knielsen/pcb_stm32f4_sram/pcb_sram.sch

## KiCad design pcb_sram.sch (2013-07-26)

Schematic: pcb_sram.sch

Parts:
B1: SWITCH_4PIN
C1, C2, C23, C24: 2.2u
C3, C20: 22p
C4, C8, C9, C10, C11, C12, C13, C14, C15, C16, C17, C18, C19, C22, C25, C27, C29, C30: 100n
C21: 4.7u
C26, C28: 1u
D1: SML-211UTT86
D2: SML-211YTT86
JP1: JUMPER3
L1: 30@100MHz
L2: 22@100MHz
P1, P2, P3, P4: DIL32
P6: CONN_3
P7: KNUSB
P8: SD_CARD
R1, R2: 1k
U1: STM32F40X_LQFP144
U2: CY62177D
U6: LP38691
X1: CRYSTAL
